DIYbioGroningen/OpenerPCR/Pictures/2014-11-14 etching for OpenerPCR/DSC05845.JPG

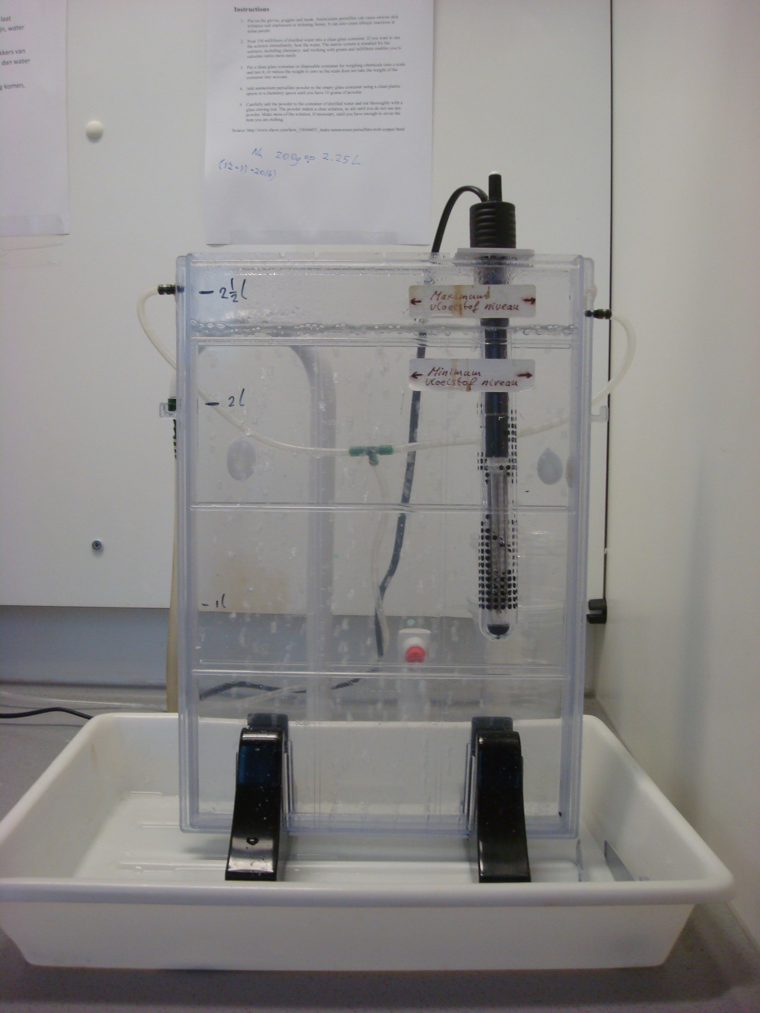
Pictures/2014-11-14 etching for OpenerPCR/DSC05845.JPG
