DIYbioGroningen/OpenerPCR/Schematic/OpenerPcr_etch_silk_top.pdf

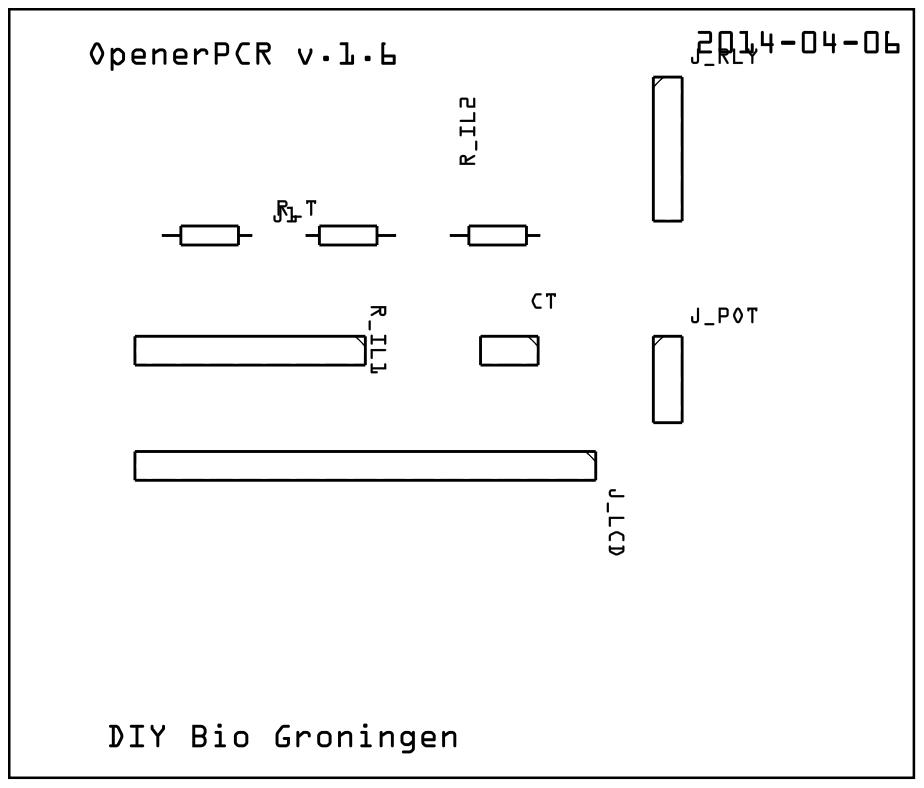
[picture p22: page 1]
