DIYbioGroningen/OpenerPCR/Schematic/OpenerPcr_etch_silk_top_mirror.pdf

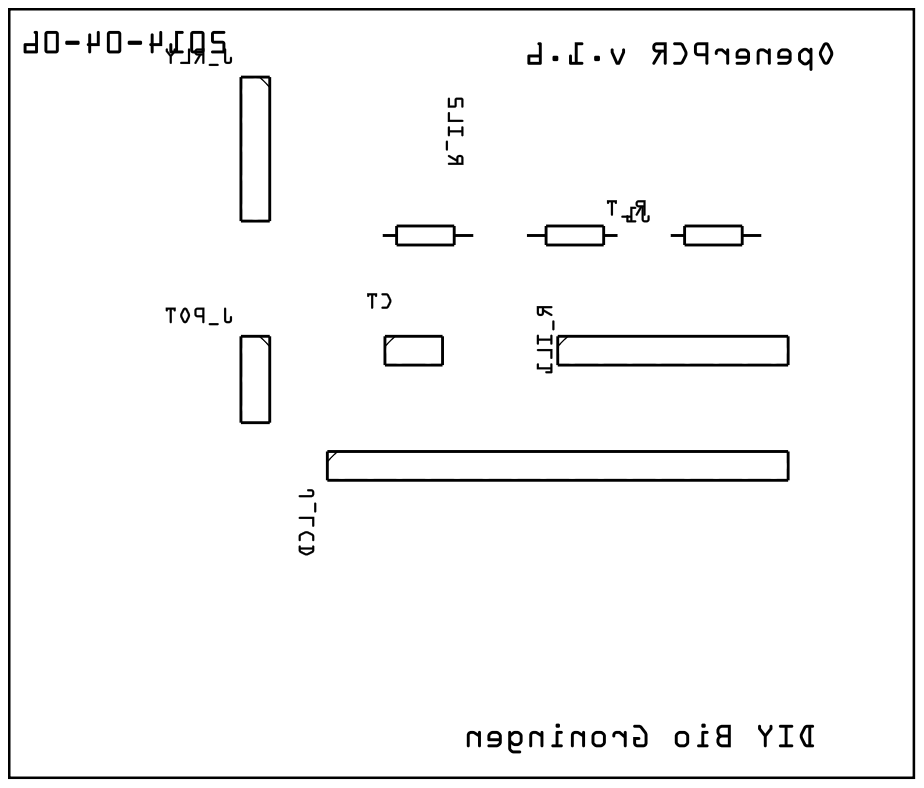
[picture p23: page 1]
